WoodyWoodsta/EEE3061WDesignProject/Code/rtos-clion/src/hal_lib.c

/**
 * ============================================================================
 * File Name          : hal_lib.c
 * Description        : Custom Hardware Abstraction Library adapted from
 *                      STM32Cube HAL
 * Authors            : Sean Wood
 *                      Adaptations from CMSIS-RTOS and the STM32Cube HAL
 * ============================================================================
 */

// == Includes ==
#include "hal_lib.h"
#include "userTasks_task.h"

// == Exported Variables ==
ADC_HandleTypeDef hadc;
DMA_HandleTypeDef hdma_adc;

SPI_HandleTypeDef hspi1;

TIM_HandleTypeDef htim1;
TIM_HandleTypeDef htim2;
TIM_HandleTypeDef htim6;
TIM_HandleTypeDef htim15;

UART_HandleTypeDef huart1;
UART_HandleTypeDef huart2;

// == Private Variables ==
DMA_HandleTypeDef hdma_usart1_tx; // TODO May not actually need these
DMA_HandleTypeDef hdma_usart2_tx;

// == Private Function Declarations ==
//static HAL_StatusTypeDef UART_EndTransmit_IT(UART_HandleTypeDef *huart); // Really not sure why I redefined this function
static int inHandlerMode(void);
HAL_StatusTypeDef cHAL_UART_Transmit_IT(UART_HandleTypeDef *huart,
    uint8_t *pData, uint16_t Size, uint8_t mSource);

// == Private Function Definitions ==
/**
 * @brief Determine whether we are in thread mode or handler mode
 * @note Not used any longer
 */
static int inHandlerMode(void) {
  return __get_IPSR() != 0;
}

///**
//* @brief  Wraps up transmission in non blocking mode.
//* @param  huart: pointer to a UART_HandleTypeDef structure that contains
//*                the configuration information for the specified UART module.
//* @retval HAL status
//*/
//static HAL_StatusTypeDef UART_EndTransmit_IT(UART_HandleTypeDef *huart) {
//  /* Disable the UART Transmit Complete Interrupt */
//  __HAL_UART_DISABLE_IT(huart, UART_IT_TC);
//
//  /* Check if a receive process is ongoing or not */
//  if (huart->State == HAL_UART_STATE_BUSY_TX_RX) {
//    huart->State = HAL_UART_STATE_BUSY_RX;
//  } else {
//    /* Disable the UART Error Interrupt: (Frame error, noise error, overrun error) */
//    __HAL_UART_DISABLE_IT(huart, UART_IT_ERR);
//
//    huart->State = HAL_UART_STATE_READY;
//  }
//
//  HAL_UART_TxCpltCallback(huart);
//
//  return HAL_OK;
//}

/**
 * @brief Send an amount of data in interrupt mode, and specify the source of the string
 * @param huart: uart handle
 * @param pData: pointer to data buffer
 * @param Size: amount of data to be sent
 * @param mSource: Whether the string was previously malloc'ed and so should be freed upon tx complete or not
 * @retval HAL status
 */
HAL_StatusTypeDef cHAL_UART_Transmit_IT(UART_HandleTypeDef *huart,
    uint8_t *pData, uint16_t Size, uint8_t mSource) {
  if ((huart->State == HAL_UART_STATE_READY)
      || (huart->State == HAL_UART_STATE_BUSY_RX)) {
    if ((pData == NULL) || (Size == 0)) {
      return HAL_ERROR;
    }

    /* Process Locked */
    __HAL_LOCK(huart);

    huart->pTxBuffPtr = pData;
    huart->TxXferSize = Size;
    huart->TxXferCount = Size;
    huart->mSource = mSource;

    huart->ErrorCode = HAL_UART_ERROR_NONE;
    /* Check if a receive process is ongoing or not */
    if (huart->State == HAL_UART_STATE_BUSY_RX) {
      huart->State = HAL_UART_STATE_BUSY_TX_RX;
    } else {
      huart->State = HAL_UART_STATE_BUSY_TX;
    }

    /* Enable the UART Error Interrupt: (Frame error, noise error, overrun error) */
    __HAL_UART_ENABLE_IT(huart, UART_IT_ERR);

    /* Process Unlocked */
    __HAL_UNLOCK(huart);

    /* Enable the UART Transmit Data Register Empty Interrupt */
    __HAL_UART_ENABLE_IT(huart, UART_IT_TXE);

    return HAL_OK;
  } else {
    return HAL_BUSY;
  }
}

// == Function Definitions ==
/**
 * @brief System clock configuration
 */
void SystemClock_Config(void) {

  RCC_OscInitTypeDef RCC_OscInitStruct;
  RCC_ClkInitTypeDef RCC_ClkInitStruct;
  RCC_PeriphCLKInitTypeDef PeriphClkInit;

  RCC_OscInitStruct.OscillatorType = RCC_OSCILLATORTYPE_HSI14
      | RCC_OSCILLATORTYPE_HSE;
  RCC_OscInitStruct.HSEState = RCC_HSE_ON;
  RCC_OscInitStruct.HSI14State = RCC_HSI14_ON;
  RCC_OscInitStruct.HSI14CalibrationValue = 16;
  RCC_OscInitStruct.PLL.PLLState = RCC_PLL_ON;
  RCC_OscInitStruct.PLL.PLLSource = RCC_PLLSOURCE_HSE;
  RCC_OscInitStruct.PLL.PLLMUL = RCC_PLL_MUL6;
  RCC_OscInitStruct.PLL.PREDIV = RCC_PREDIV_DIV1;
  HAL_RCC_OscConfig(&RCC_OscInitStruct);

  RCC_ClkInitStruct.ClockType = RCC_CLOCKTYPE_SYSCLK;
  RCC_ClkInitStruct.SYSCLKSource = RCC_SYSCLKSOURCE_PLLCLK;
  RCC_ClkInitStruct.AHBCLKDivider = RCC_SYSCLK_DIV1;
  RCC_ClkInitStruct.APB1CLKDivider = RCC_HCLK_DIV1;
  HAL_RCC_ClockConfig(&RCC_ClkInitStruct, FLASH_LATENCY_1);

  PeriphClkInit.PeriphClockSelection = RCC_PERIPHCLK_USART1;
  PeriphClkInit.Usart1ClockSelection = RCC_USART1CLKSOURCE_PCLK1;
  HAL_RCCEx_PeriphCLKConfig(&PeriphClkInit);

  HAL_SYSTICK_Config(HAL_RCC_GetHCLKFreq() / 1000);

  HAL_SYSTICK_CLKSourceConfig(SYSTICK_CLKSOURCE_HCLK);

}

/**
 * @brief ADC init function
 */
void MX_ADC_Init(void) {

  ADC_ChannelConfTypeDef sConfig;

  /**Configure the global features of the ADC (Clock, Resolution, Data Alignment and number of conversion)
   */
  hadc.Instance = ADC1;
  hadc.Init.ClockPrescaler = ADC_CLOCK_ASYNC;
  hadc.Init.Resolution = ADC_RESOLUTION12b;
  hadc.Init.DataAlign = ADC_DATAALIGN_RIGHT;
  hadc.Init.ScanConvMode = ADC_SCAN_DIRECTION_FORWARD;
  hadc.Init.EOCSelection = EOC_SINGLE_CONV;
  hadc.Init.LowPowerAutoWait = DISABLE;
  hadc.Init.LowPowerAutoPowerOff = DISABLE;
  hadc.Init.ContinuousConvMode = ENABLE;
  hadc.Init.DiscontinuousConvMode = DISABLE;
  hadc.Init.ExternalTrigConvEdge = ADC_EXTERNALTRIGCONVEDGE_NONE;
  hadc.Init.DMAContinuousRequests = DISABLE;
  hadc.Init.Overrun = OVR_DATA_PRESERVED;
  HAL_ADC_Init(&hadc);

  /**Configure for the selected ADC regular channel to be converted.
   */
  sConfig.Channel = ADC_CHANNEL_9;
  sConfig.Rank = ADC_RANK_CHANNEL_NUMBER;
  sConfig.SamplingTime = ADC_SAMPLETIME_55CYCLES_5;
  HAL_ADC_ConfigChannel(&hadc, &sConfig);

}

/**
 * @brief SPI1 init function (Gyro)
 */
void MX_SPI1_Init(void) {

  hspi1.Instance = SPI1;
  hspi1.Init.Mode = SPI_MODE_MASTER;
  hspi1.Init.Direction = SPI_DIRECTION_2LINES;
  hspi1.Init.DataSize = SPI_DATASIZE_8BIT;
  hspi1.Init.CLKPolarity = SPI_POLARITY_LOW;
  hspi1.Init.CLKPhase = SPI_PHASE_1EDGE;
  hspi1.Init.NSS = SPI_NSS_SOFT;
  hspi1.Init.BaudRatePrescaler = SPI_BAUDRATEPRESCALER_256;
  hspi1.Init.FirstBit = SPI_FIRSTBIT_MSB;
  hspi1.Init.TIMode = SPI_TIMODE_DISABLED;
  hspi1.Init.CRCCalculation = SPI_CRCCALCULATION_ENABLED;
  hspi1.Init.CRCPolynomial = 10;
  hspi1.Init.CRCLength = SPI_CRC_LENGTH_DATASIZE;
  hspi1.Init.NSSPMode = SPI_NSS_PULSE_ENABLED;
  HAL_SPI_Init(&hspi1);

}

/**
 * @brief TIM1 init function
 * @Note TODO Put channel info here
 */
void MX_TIM1_Init(void) {

  TIM_MasterConfigTypeDef sMasterConfig;
  TIM_BreakDeadTimeConfigTypeDef sBreakDeadTimeConfig;
  TIM_OC_InitTypeDef sConfigOC;

  htim1.Instance = TIM1;
  htim1.Init.Prescaler = 48;
  htim1.Init.CounterMode = TIM_COUNTERMODE_UP;
  htim1.Init.Period = 1000;
  htim1.Init.ClockDivision = TIM_CLOCKDIVISION_DIV1;
  htim1.Init.RepetitionCounter = 0;
  HAL_TIM_PWM_Init(&htim1);

  sMasterConfig.MasterOutputTrigger = TIM_TRGO_RESET;
  sMasterConfig.MasterSlaveMode = TIM_MASTERSLAVEMODE_DISABLE;
  HAL_TIMEx_MasterConfigSynchronization(&htim1, &sMasterConfig);

  sBreakDeadTimeConfig.OffStateRunMode = TIM_OSSR_DISABLE;
  sBreakDeadTimeConfig.OffStateIDLEMode = TIM_OSSI_DISABLE;
  sBreakDeadTimeConfig.LockLevel = TIM_LOCKLEVEL_OFF;
  sBreakDeadTimeConfig.DeadTime = 0;
  sBreakDeadTimeConfig.BreakState = TIM_BREAK_DISABLE;
  sBreakDeadTimeConfig.BreakPolarity = TIM_BREAKPOLARITY_HIGH;
  sBreakDeadTimeConfig.AutomaticOutput = TIM_AUTOMATICOUTPUT_DISABLE;
  HAL_TIMEx_ConfigBreakDeadTime(&htim1, &sBreakDeadTimeConfig);

  sConfigOC.OCMode = TIM_OCMODE_PWM1;
  sConfigOC.Pulse = 0;
  sConfigOC.OCPolarity = TIM_OCPOLARITY_HIGH;
  sConfigOC.OCNPolarity = TIM_OCNPOLARITY_HIGH;
  sConfigOC.OCFastMode = TIM_OCFAST_DISABLE;
  sConfigOC.OCIdleState = TIM_OCIDLESTATE_RESET;
  sConfigOC.OCNIdleState = TIM_OCNIDLESTATE_RESET;
  HAL_TIM_PWM_ConfigChannel(&htim1, &sConfigOC, TIM_CHANNEL_1);

#ifndef JG_BOARD // If we are not using James' Board
  HAL_TIM_PWM_ConfigChannel(&htim1, &sConfigOC, TIM_CHANNEL_2);
  HAL_TIM_PWM_ConfigChannel(&htim1, &sConfigOC, TIM_CHANNEL_3);
#endif

  HAL_TIM_PWM_ConfigChannel(&htim1, &sConfigOC, TIM_CHANNEL_4);
}

/**
 * @brief TIM2 init function
 * @Note TODO Put channel info here
 */
void MX_TIM2_Init(void) {

  TIM_MasterConfigTypeDef sMasterConfig;
  TIM_OC_InitTypeDef sConfigOC;

  htim2.Instance = TIM2;
  htim2.Init.Prescaler = 48;
  htim2.Init.CounterMode = TIM_COUNTERMODE_UP;
  htim2.Init.Period = 1000;
  htim2.Init.ClockDivision = TIM_CLOCKDIVISION_DIV1;
  HAL_TIM_PWM_Init(&htim2);

  sMasterConfig.MasterOutputTrigger = TIM_TRGO_RESET;
  sMasterConfig.MasterSlaveMode = TIM_MASTERSLAVEMODE_DISABLE;
  HAL_TIMEx_MasterConfigSynchronization(&htim2, &sMasterConfig);

  sConfigOC.OCMode = TIM_OCMODE_PWM1;
  sConfigOC.Pulse = 0;
  sConfigOC.OCPolarity = TIM_OCPOLARITY_HIGH;
  sConfigOC.OCFastMode = TIM_OCFAST_DISABLE;
  sConfigOC.OCIdleState = TIM_OCIDLESTATE_RESET;
  HAL_TIM_PWM_ConfigChannel(&htim2, &sConfigOC, TIM_CHANNEL_3);

}

/**
 * @brief TIM15 init function
 * @Note TODO Put channel info here
 */
void MX_TIM15_Init(void) {

  TIM_MasterConfigTypeDef sMasterConfig;
  TIM_BreakDeadTimeConfigTypeDef sBreakDeadTimeConfig;
  TIM_OC_InitTypeDef sConfigOC;

  htim15.Instance = TIM15;
  htim15.Init.Prescaler = 48;
  htim15.Init.CounterMode = TIM_COUNTERMODE_UP;
  htim15.Init.Period = 1000;
  htim15.Init.ClockDivision = TIM_CLOCKDIVISION_DIV1;
  htim15.Init.RepetitionCounter = 0;
  HAL_TIM_PWM_Init(&htim15);

  sMasterConfig.MasterOutputTrigger = TIM_TRGO_RESET;
  sMasterConfig.MasterSlaveMode = TIM_MASTERSLAVEMODE_DISABLE;
  HAL_TIMEx_MasterConfigSynchronization(&htim15, &sMasterConfig);

  sBreakDeadTimeConfig.OffStateRunMode = TIM_OSSR_DISABLE;
  sBreakDeadTimeConfig.OffStateIDLEMode = TIM_OSSI_DISABLE;
  sBreakDeadTimeConfig.LockLevel = TIM_LOCKLEVEL_OFF;
  sBreakDeadTimeConfig.DeadTime = 0;
  sBreakDeadTimeConfig.BreakState = TIM_BREAK_DISABLE;
  sBreakDeadTimeConfig.BreakPolarity = TIM_BREAKPOLARITY_HIGH;
  sBreakDeadTimeConfig.AutomaticOutput = TIM_AUTOMATICOUTPUT_DISABLE;
  HAL_TIMEx_ConfigBreakDeadTime(&htim15, &sBreakDeadTimeConfig);

  sConfigOC.OCMode = TIM_OCMODE_PWM1;
  sConfigOC.Pulse = 0;
  sConfigOC.OCPolarity = TIM_OCPOLARITY_HIGH;
  sConfigOC.OCNPolarity = TIM_OCNPOLARITY_HIGH;
  sConfigOC.OCFastMode = TIM_OCFAST_DISABLE;
  sConfigOC.OCIdleState = TIM_OCIDLESTATE_RESET;
  sConfigOC.OCNIdleState = TIM_OCNIDLESTATE_RESET;
  HAL_TIM_PWM_ConfigChannel(&htim15, &sConfigOC, TIM_CHANNEL_1);

  HAL_TIM_PWM_ConfigChannel(&htim15, &sConfigOC, TIM_CHANNEL_2);

}

/* USART1 init function */
void MX_USART1_UART_Init(void) {

  huart1.Instance = USART1;
  huart1.Init.BaudRate = 115200;
  huart1.Init.WordLength = UART_WORDLENGTH_8B;
  huart1.Init.StopBits = UART_STOPBITS_1;
  huart1.Init.Parity = UART_PARITY_NONE;
  huart1.Init.Mode = UART_MODE_TX_RX;
  huart1.Init.HwFlowCtl = UART_HWCONTROL_NONE;
  huart1.Init.OverSampling = UART_OVERSAMPLING_16;
  huart1.Init.OneBitSampling = UART_ONEBIT_SAMPLING_DISABLED;
  huart1.AdvancedInit.AdvFeatureInit = UART_ADVFEATURE_NO_INIT;
  HAL_UART_Init(&huart1);

}

/**
 * @brief USART2 (WIFI) Initialisation Function
 */
void MX_USART2_UART_Init(void) {

  huart2.Instance = USART2;
  huart2.Init.BaudRate = 115200;
  huart2.Init.WordLength = UART_WORDLENGTH_8B;
  huart2.Init.StopBits = UART_STOPBITS_1;
  huart2.Init.Parity = UART_PARITY_NONE;
  huart2.Init.Mode = UART_MODE_TX_RX;
  huart2.Init.HwFlowCtl = UART_HWCONTROL_NONE;
  huart2.Init.OverSampling = UART_OVERSAMPLING_16;
  huart2.Init.OneBitSampling = UART_ONEBIT_SAMPLING_DISABLED;
  huart2.AdvancedInit.AdvFeatureInit = UART_ADVFEATURE_NO_INIT;
  HAL_UART_Init(&huart2);

}

/**
 * @brief DMA controller clock Initialisation
 * @note Not used any longer
 */
void MX_DMA_Init(void) {
  /* DMA controller clock enable */
  __DMA1_CLK_ENABLE()
  ;

  /* DMA interrupt init */
  HAL_NVIC_SetPriority(DMA1_Channel1_IRQn, 3, 0);
  HAL_NVIC_EnableIRQ(DMA1_Channel1_IRQn);

}

/* TIM6 init function */
void MX_TIM6_Init(void)
{
  __HAL_RCC_TIM6_CLK_ENABLE();
  TIM_MasterConfigTypeDef sMasterConfig;

  htim6.Instance = TIM6;
  htim6.Init.Prescaler = 5000;
  htim6.Init.CounterMode = TIM_COUNTERMODE_UP;
  htim6.Init.Period = 0xffff;
  HAL_TIM_Base_Init(&htim6);

  sMasterConfig.MasterOutputTrigger = TIM_TRGO_RESET;
  sMasterConfig.MasterSlaveMode = TIM_MASTERSLAVEMODE_DISABLE;
  HAL_TIMEx_MasterConfigSynchronization(&htim6, &sMasterConfig);

  __HAL_TIM_ENABLE(&htim6);

}

/** Configure pins as
 * Analog
 * Input
 * Output
 * EVENT_OUT
 * EXTI
 */
void MX_GPIO_Init(void) {

  GPIO_InitTypeDef GPIO_InitStruct;

  /* GPIO Ports Clock Enable */
  __GPIOF_CLK_ENABLE()
  ;
  __GPIOA_CLK_ENABLE()
  ;
  __GPIOB_CLK_ENABLE()
  ;

  /*Configure GPIO pins : PA0 PA1 */
  GPIO_InitStruct.Pin = GPIO_PIN_0 | GPIO_PIN_1;
  GPIO_InitStruct.Mode = GPIO_MODE_IT_RISING_FALLING;
  GPIO_InitStruct.Pull = GPIO_PULLUP;
  HAL_GPIO_Init(GPIOA, &GPIO_InitStruct);

  /*Configure GPIO pin : PB12 - Reed switch */
  GPIO_InitStruct.Pin = GPIO_PIN_12;
  GPIO_InitStruct.Mode = GPIO_MODE_INPUT;
  GPIO_InitStruct.Pull = GPIO_PULLUP;
  HAL_GPIO_Init(GPIOB, &GPIO_InitStruct);

  /*Configure GPIO pins : PA4 PA12 */
  GPIO_InitStruct.Pin = GPIO_PIN_4 | GPIO_PIN_12;
  GPIO_InitStruct.Mode = GPIO_MODE_OUTPUT_PP;
  GPIO_InitStruct.Pull = GPIO_NOPULL;
  GPIO_InitStruct.Speed = GPIO_SPEED_HIGH;
  HAL_GPIO_Init(GPIOA, &GPIO_InitStruct);

  /*Configure GPIO pins : PB0 PB2 PB13 */
  GPIO_InitStruct.Pin = GPIO_PIN_0 | GPIO_PIN_2 | GPIO_PIN_13;
  GPIO_InitStruct.Mode = GPIO_MODE_OUTPUT_PP;
  GPIO_InitStruct.Pull = GPIO_NOPULL;
  GPIO_InitStruct.Speed = GPIO_SPEED_HIGH;
  HAL_GPIO_Init(GPIOB, &GPIO_InitStruct);

  /*Configure GPIO pin : PF6 */
  GPIO_InitStruct.Pin = GPIO_PIN_6;
  GPIO_InitStruct.Mode = GPIO_MODE_OUTPUT_PP;
  GPIO_InitStruct.Pull = GPIO_NOPULL;
  GPIO_InitStruct.Speed = GPIO_SPEED_HIGH;
  HAL_GPIO_Init(GPIOF, &GPIO_InitStruct);

  /*Configure GPIO pins : PB3 PB4 PB5 */
  GPIO_InitStruct.Pin = GPIO_PIN_3 | GPIO_PIN_4 | GPIO_PIN_5;
  GPIO_InitStruct.Mode = GPIO_MODE_INPUT;
  GPIO_InitStruct.Pull = GPIO_NOPULL;
  HAL_GPIO_Init(GPIOB, &GPIO_InitStruct);

  /* EXTI interrupt init*/
  HAL_NVIC_SetPriority(EXTI0_1_IRQn, 3, 0);
  HAL_NVIC_EnableIRQ(EXTI0_1_IRQn);
}

// == USART Receive via IT Custom Driver ==
/**
 * @brief Receive data, in interrupt mode (non-blocking), up until a terminator
 * @param *huart: Pointer to UART handle
 * @param pData: pointer to data buffer
 * @retval HAL status
 */
HAL_StatusTypeDef cHAL_UART_TermReceive_IT(UART_HandleTypeDef *huart,
    uint16_t MaxSize) {
  if ((huart->State == HAL_UART_STATE_READY)
      || (huart->State == HAL_UART_STATE_BUSY_TX)) {

    /* Process Locked */
    __HAL_LOCK(huart);

    huart->pRxBuffPtr = NULL;
    huart->RxXferMaxSize = MaxSize; // Maximum dynamically allocated buffer
    huart->RxXferSize = 0; // Current memory buffer size
    huart->RxXferCount = 0; // Count of how many characters are in current buffer

    /* Computation of UART mask to apply to RDR register */
    __HAL_UART_MASK_COMPUTATION(huart);

    huart->ErrorCode = HAL_UART_ERROR_NONE;
    /* Check if a transmit process is ongoing or not */
    if (huart->State == HAL_UART_STATE_BUSY_TX) {
      huart->State = HAL_UART_STATE_BUSY_TX_RX;
    } else {
      huart->State = HAL_UART_STATE_BUSY_RX;
    }

    /* Enable the UART Parity Error Interrupt */
    __HAL_UART_ENABLE_IT(huart, UART_IT_PE);

    /* Enable the UART Error Interrupt: (Frame error, noise error, overrun error) */
    __HAL_UART_ENABLE_IT(huart, UART_IT_ERR);

    /* Process Unlocked */
    __HAL_UNLOCK(huart);

    /* Enable the UART Data Register not empty Interrupt */
    __HAL_UART_ENABLE_IT(huart, UART_IT_RXNE);

    return HAL_OK;
  } else {
    return HAL_BUSY;
  }
}

/**
 * @brief This function handles UART interrupt request for "Receive via IT" Custom Driver.
 * @param *huart: Pointer to UART handle
 * @retval None
 */
void cHAL_UART_IRQTermHandler(UART_HandleTypeDef *huart) {
  /* UART parity error interrupt occurred -------------------------------------*/
  if ((__HAL_UART_GET_IT(huart, UART_IT_PE) != RESET)
      && (__HAL_UART_GET_IT_SOURCE(huart, UART_IT_PE) != RESET)) {
    __HAL_UART_CLEAR_IT(huart, UART_CLEAR_PEF);

    huart->ErrorCode |= HAL_UART_ERROR_PE;
    /* Set the UART state ready to be able to start again the process */
    huart->State = HAL_UART_STATE_READY;
  }

  /* UART frame error interrupt occured --------------------------------------*/
  if ((__HAL_UART_GET_IT(huart, UART_IT_FE) != RESET)
      && (__HAL_UART_GET_IT_SOURCE(huart, UART_IT_ERR) != RESET)) {
    __HAL_UART_CLEAR_IT(huart, UART_CLEAR_FEF);

    huart->ErrorCode |= HAL_UART_ERROR_FE;
    /* Set the UART state ready to be able to start again the process */
    huart->State = HAL_UART_STATE_READY;
  }

  /* UART noise error interrupt occured --------------------------------------*/
  if ((__HAL_UART_GET_IT(huart, UART_IT_NE) != RESET)
      && (__HAL_UART_GET_IT_SOURCE(huart, UART_IT_ERR) != RESET)) {
    __HAL_UART_CLEAR_IT(huart, UART_CLEAR_NEF);

    huart->ErrorCode |= HAL_UART_ERROR_NE;
    /* Set the UART state ready to be able to start again the process */
    huart->State = HAL_UART_STATE_READY;
  }

  /* UART Over-Run interrupt occured -----------------------------------------*/
  if ((__HAL_UART_GET_IT(huart, UART_IT_ORE) != RESET)
      && (__HAL_UART_GET_IT_SOURCE(huart, UART_IT_ERR) != RESET)) {
    __HAL_UART_CLEAR_IT(huart, UART_CLEAR_OREF);

    huart->ErrorCode |= HAL_UART_ERROR_ORE;
    /* Set the UART state ready to be able to start again the process */
    huart->State = HAL_UART_STATE_READY;
  }

  /* Call UART Error Call back function if need be --------------------------*/
  if (huart->ErrorCode != HAL_UART_ERROR_NONE) {
    HAL_UART_ErrorCallback(huart);
  }

#if !defined(STM32F030x6) && !defined(STM32F030x8)&& !defined(STM32F070xB)&& !defined(STM32F070x6)&& !defined(STM32F030xC)
  /* UART wakeup from Stop mode interrupt occurred -------------------------------------*/
  if ((__HAL_UART_GET_IT(huart, UART_IT_WUF) != RESET)
      && (__HAL_UART_GET_IT_SOURCE(huart, UART_IT_WUF) != RESET)) {
    __HAL_UART_CLEAR_IT(huart, UART_CLEAR_WUF);
    /* Set the UART state ready to be able to start again the process */
    huart->State = HAL_UART_STATE_READY;
    HAL_UART_WakeupCallback(huart);
  }
#endif /* !defined(STM32F030x6) && !defined(STM32F030x8)&& !defined(STM32F070xB)&& !defined(STM32F070x6)&& !defined(STM32F030xC) */

  /* UART in mode Receiver ---------------------------------------------------*/
  if ((__HAL_UART_GET_IT(huart, UART_IT_RXNE) != RESET)
      && (__HAL_UART_GET_IT_SOURCE(huart, UART_IT_RXNE) != RESET)) {
    HAL_StatusTypeDef status = cUART_TermReceive_IT(huart);

    /* Clear RXNE interrupt flag */
    __HAL_UART_SEND_REQ(huart, UART_RXDATA_FLUSH_REQUEST);
  }

  /* UART in mode Transmitter ------------------------------------------------*/
  if ((__HAL_UART_GET_IT(huart, UART_IT_TXE) != RESET)
      && (__HAL_UART_GET_IT_SOURCE(huart, UART_IT_TXE) != RESET)) {
    UART_Transmit_IT(huart);
  }

  /* UART in mode Transmitter ------------------------------------------------*/
  if ((__HAL_UART_GET_IT(huart, UART_IT_TC) != RESET)
      && (__HAL_UART_GET_IT_SOURCE(huart, UART_IT_TC) != RESET)) {
    UART_EndTransmit_IT(huart);
  }
}

/**
 * @brief Receive data, in interrupt mode (non-blocking), up until a terminator (data transfer)
 *         Function called for every byte under interruption only, once
 *         interruptions have been enabled by HAL_UART_Receive_IT()
 *         Terminators included in the received buffer
 * @param  *huart: Pointer to UART handle
 * @retval HAL status
 */
HAL_StatusTypeDef cUART_TermReceive_IT(UART_HandleTypeDef *huart) {
  uint16_t uhMask = huart->Mask;
  uint16_t rxXferSize = huart->RxXferSize; // Total allocated string buffer length
  uint16_t rxXferCount = huart->RxXferCount;

  // Check state of USART (NOTE: HAL_UART_STATE_READY implies there was an error, but this should not halt ransfer)
  if ((huart->State == HAL_UART_STATE_BUSY_TX_RX)
      || (huart->State == HAL_UART_STATE_BUSY_RX)
      || (huart->State == HAL_UART_STATE_READY)) {

    // Grab the character from the receive data register
    uint8_t inChar = (uint8_t) (huart->Instance->RDR & (uint8_t) uhMask);

    // If we have run out of buffer, "re-allocate" some more (dynamic allocation-re-allocation)
    if (rxXferCount == rxXferSize) {
      // Increment the current buffer size by 16 bytes
      rxXferSize += USART_DYNAMIC_BUFFER_INCREMENT;

      // Create a new pointer and allocate the new memory required
      uint8_t *pNew = pvPortMalloc(rxXferSize);

      // Copy in and free the existing buffer, only if this is not the first allocation of the string
      // NOTE: This is because the pointer to the previous string may still be used elsewhere
      if (rxXferSize != USART_DYNAMIC_BUFFER_INCREMENT) {
        memcpy(pNew, huart->pRxBuffPtr, rxXferCount);
        vPortFree(huart->pRxBuffPtr);
      }

      // Re-assign the handle's rx buffer pointer to the new pointer and update total string buffer length
      huart->pRxBuffPtr = pNew;
      huart->RxXferSize = rxXferSize;
    }

    huart->pRxBuffPtr[rxXferCount] = (uint8_t) inChar;
    huart->RxXferCount = ++rxXferCount; // Update the receive count
    // At this stage, huart->RxXferCount reflects the number of bytes in the buffer

    // If we have reached a <cr>, <lf> or NULL, or if we have reached the end of the largest buffer, send off a completed string
    if ((inChar == 0x0A) || (rxXferCount == huart->RxXferMaxSize)) {

      // If the string is more than just a <cr><lf>, fire the receive complete callback
      if (rxXferCount > 2) {
        HAL_UART_RxCpltCallback(huart);
      } else {
        // Else we should free the existing buffer, if it exists!
        if (rxXferCount != 0) {
          vPortFree(huart->pRxBuffPtr);
        }
      }

      // Reset string and buffer count
      huart->RxXferCount = 0;
      huart->RxXferSize = 0;

      // Exit the story here
      return HAL_OK;
    }

    return HAL_OK;
  } else {
    return HAL_BUSY;

  }
}

/**
 * @brief Transmit data out of the UART via Interrupts safely (i.e. without stomping existing transmissions)
 * NOTE: This can still be called in interrupts due to the check
 * @param *huart: Pointer to UART handle
 * @param *pData: Pointer to the data to transmit
 * @param size: Size of the data to transmit
 * @retval HAL status
 */
HAL_StatusTypeDef cHAL_USART_sTransmit_IT(UART_HandleTypeDef *huart,
    uint8_t *pData, uint16_t size, uint8_t mSource) {
  HAL_StatusTypeDef txStatus = HAL_BUSY;

  while (1) {
    txStatus = cHAL_UART_Transmit_IT(huart, pData, size, mSource);

    // If we are in thread mode, wait on HAL_BUSY, else just return the status
    if (!inHandlerMode()) {
      // Check for OK to prevent other checks, else check for errors
      if (txStatus != HAL_BUSY) {
        return txStatus;
      }
    } else {
      return txStatus;
    }

    osDelay(5);
  }
}

/**
 * @brief USART callback on receiving a completed string (terminated)
 *        This callback is hardcoded to send the string pointer in a string message to USARTInTask
 * @param *huart: Pointer to UART handle
 */
void HAL_UART_RxCpltCallback(UART_HandleTypeDef *huart) {
  msg_stringMessage_t *pTxStringMessage;
  pTxStringMessage = osPoolAlloc(strBufMPool);

  // Fill the string message
  pTxStringMessage->pString = huart->pRxBuffPtr;
  pTxStringMessage->stringLength = huart->RxXferCount;

  // Identify source
  if (huart->Instance == USART1_BASE) {
    pTxStringMessage->messageSource = MSG_SRC_USB;
  } else {
    pTxStringMessage->messageSource = MSG_SRC_WIFI;
  }

  // Send the string message to the USARTInTask
  osStatus status = osMessagePut(msgQUSARTIn, (uint32_t) pTxStringMessage, 0);

  // If the send failed, free the relevant memory
  if (status != osOK) {
    vPortFree(pTxStringMessage->pString);
    osPoolFree(strBufMPool, pTxStringMessage);
  }
}

/**
 * @brief USART callback on transmitting a completed string (terminated)
 * @param *huart: Pointer to UART handle
 */
void HAL_UART_TxCpltCallback(UART_HandleTypeDef *huart) {
  // If the string is marked to be freed
  if (huart->mSource) {
    // Free the memory held by the string during transmit
    vPortFree(huart->pTxBuffPtr - huart->TxXferSize);
  }
}

/**
 * @brief USART callback on TX or RX error
 * @param *huart: Pointer to UART handle
 */
void HAL_UART_ErrorCallback(UART_HandleTypeDef *huart) {
  HAL_GPIO_WritePin(GPIOB, GPIO_PIN_7, SET);
}
