WoodyWoodsta/EEE3061WDesignProject/Code/rtos-clion/include/genericMessaging_lib.h

/**
  * ============================================================================
  * File Name          : genericMessaging_lib.h
  * Description        : Generic messaging system header file
  * Author             : Sean Wood
  * ============================================================================
  */

#ifndef GENERICMESSAGING_LIB_H
#define GENERICMESSAGING_LIB_H

// == Includes ==
#include "cmsis_os.h"
#include "hal_lib.h"
#include "string.h"

// == Definitions ==
#define MRSP_NO_HANDLE 0 // Do not let the library handle the data memory
#define MRSP_HANDLE 1 // Let the library handle the data memory

#define GLOBAL_MESSAGE_MPOOL_SIZE   30 // Maximum number of messages that can exist in memory
#define STRING_BUFFER_MPOOL_SIZE    10 // Maximum number of string buffer pointer messages that can exist in memory

// == Type Definitions ==
// Types of messages
typedef enum {
  MSG_TYPE_NO_MESSAGE,
  MSG_TYPE_STRING,
  MSG_TYPE_COORDS,
  MSG_TYPE_COMMAND
} msgType_t;

// Sources of messages
typedef enum {
  MSG_SRC_USB,
  MSG_SRC_WIFI,
  MSG_SRC_USART_IN_TASK,
  MSG_SRC_USART_OUT_TASK,
  MSG_SRC_BOSS_TASK,
  MSG_SRC_MOTOR_TASK,
  MSG_SRC_LINE_SENSOR_TASK,
  MSG_SRC_USER_IO_TASK
} msgSource_t;

// Commands
typedef enum {
  MSG_CMD_NO_CMD,
  MSG_CMD_WIFI_TEST_AT,
  MSG_CMD_WIFI_INIT,
  MSG_CMD_WIFI_CONNECT_AP,
  MSG_CMD_WIFI_TX_AT,
  MSG_CMD_WIFI_TX_ATE_0,
  MSG_CMD_WIFI_TX_CWMODE_3,
  MSG_CMD_WIFI_TX_CIPMUX_1,
  MSG_CMD_WIFI_TX_CONNECT_AP,
  MSG_CMD_WIFI_TX_START_SERVER,
  MSG_CMD_WIFI_RX_OK,
  MSG_CMD_WIFI_RX_NO_CHANGE,
  MSG_CMD_WIFI_RX_ERROR,
  MSG_CMD_WIFI_RX_NO_FUNCTION,
  MSG_CMD_WIFI_RX_FAIL,
  MSG_CMD_WIFI_RX_START_SERVER,
  MSG_CMD_LED_ON,
  MSG_CMD_LED_OFF,
  MSG_CMD_LED_BLINK_SLOW,
  MSG_CMD_LED_BLINK_FAST,
  MSG_CMD_LED_BLINK_SUPERFAST,
  MSG_CMD_BUZZER_ON,
  MSG_CMD_BUZZER_OFF,
  MSG_CMD_BUZZER_BURST_ONCE,
  MSG_CMD_BUZZER_BURST_TWICE,
  MSG_CMD_BUZZER_BURST_THRICE,
  MSG_CMD_BUZZER_PULSE_SLOW,
  MSG_CMD_BUZZER_PULSE_FAST,
  MSG_CMD_SW0_DOWN,
  MSG_CMD_SW0_UP,
  MSG_CMD_SW1_DOWN,
  MSG_CMD_SW1_UP
} msgCommand_t;

// Generic message struct to package any associated data
typedef struct {
  msgType_t messageType; // Type of message data
  msgSource_t messageSource; // Where did this message come from
  uint8_t mRsp; // Data memory responsibility
  uint32_t dataLength; // Length of the data
  void *pData; // Pointer to data TODO Rename this to dataPtr
} msg_genericMessage_t;

// String pointer message struct to be used for sending to the USART In Task
typedef struct {
  msgSource_t messageSource; // Where did this message come from
  uint16_t stringLength; // Length of the string
  uint8_t *pString; // Pointer to string
} msg_stringMessage_t;

// == Message Data Structures ==
// NOTE: All message types named: data_<type of data>_t

// String data struct
typedef struct {
  msgType_t messageType;
  uint16_t stringLength;
  uint8_t *pString;
} data_string_t;

// Co-ordinate data struct
typedef struct {
  msgType_t messageType;
  uint16_t x;
  uint16_t y;
  uint16_t z;
} data_coords_t;

// Command data struct
typedef struct {
  msgType_t messageType;
  msgCommand_t command;
} data_command_t;

// == Declarations ==
osPoolId genericMPool;
osPoolId strBufMPool;

// == Function Prototypes ==
void sendMessage(osMessageQId msgQ, msgType_t type, msgSource_t source, uint8_t mRsp, void *data, uint32_t timeout);
void sendCommand(osMessageQId msgQ, msgSource_t source, msgCommand_t command, uint32_t timeout);
void fetchMessage(osMessageQId msgQ, msg_genericMessage_t *messagePtr, uint32_t timeout);
void *decodeMessage(msg_genericMessage_t *messagePtr, void *dataStruct);
msgCommand_t decodeCommand(msg_genericMessage_t *messagePtr);

#endif /*GENERICMESSAGING_LIB_H*/
