WoodyWoodsta/EEE3061WDesignProject/Code/rtos-clion/include/strings_res.h

/**
* ============================================================================
* File Name          : strings_res.h
* Description        : String resource header file
* Author             : Sean Wood
* ============================================================================
*/

// == Includes ==
#include "stm32f0xx_hal.h" // For data types

// == Exported Variables ==
extern const uint8_t txString_ATCommandTest[];
extern const uint8_t txString_ATE0[];
extern const uint8_t txString_stationMode3[];
extern const uint8_t txString_multiConnect1[];
extern const uint8_t txString_startServer[];
extern const uint8_t txString_OKReceived[];
extern const uint8_t txString_ATCommandTestError[];
extern const uint8_t txString_wifiInitialised[];
extern const uint8_t txString_wifiInitError[];
extern const uint8_t txString_wifiConnected[];
extern const uint8_t txString_wifiServerStarted[];
extern const uint8_t txString_commStateManual[];
extern const uint8_t txString_commStateAuto[];
extern const uint8_t txString_connectAPCommand[];
extern const uint8_t txString_linePosCenter[];
extern const uint8_t txString_linePosLeft[];
extern const uint8_t txString_linePosRight[];
extern const uint8_t txString_linePosLeftLeft[];
extern const uint8_t txString_linePosRightRight[];

extern const uint8_t rxString_led0Toggle[];
extern const uint8_t rxString_commStateManual[];
extern const uint8_t rxString_commStateAuto[];
extern const uint8_t rxString_ATCommandTest[];
extern const uint8_t rxString_wifiInit[];
extern const uint8_t rxString_wifiConnectAp[];
extern const uint8_t rxString_wifiStartServer[];
extern const uint8_t rxString_OK[];
extern const uint8_t rxString_error[];
extern const uint8_t rxString_noSuchFunction[];
extern const uint8_t rxString_noChange[];
extern const uint8_t rxString_fail[];
extern const uint8_t rxString_receiveDataCommand[];
extern const uint8_t rxString_link[];
extern const uint8_t rxString_unlink[];
extern const uint8_t rxString_WFR[];
extern const uint8_t rxString_WFS[];
extern const uint8_t rxString_WFL[];
